davinunes/TopLifeMiami-Nivel-de-gua/imagens/Screenshot_8.png

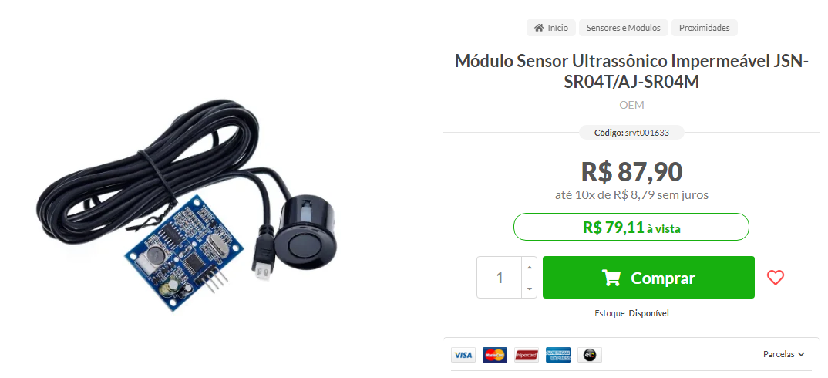
imagens/Screenshot_8.png
