davinunes/TopLifeMiami-Nivel-de-gua/imagens/Screenshot_27.png

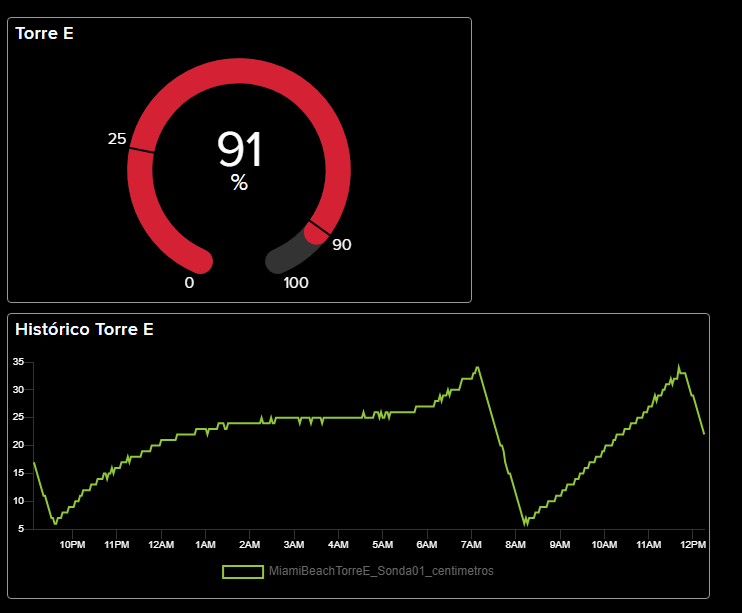
imagens/Screenshot_27.png
